EMariotte/MecanumRobot/hardware/MecanumRobot_v1.1/Schematic/MCU.kicad_sch

## KiCad design hardware/MecanumRobot_v1.1/Schematic/MCU.kicad_sch (2026-06-23)

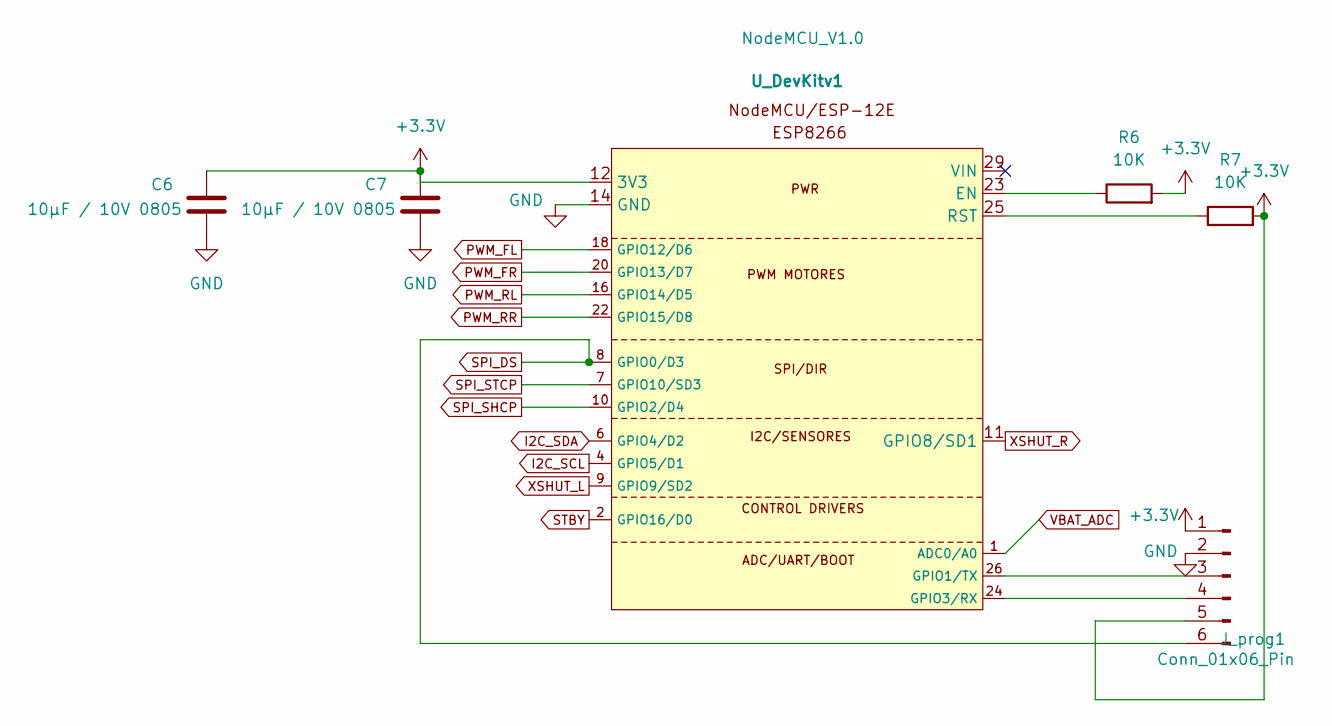
[picture p2: schematic MCU.kicad_sch]

Parts:
C6, C7: 10µF / 10V 0805; C_0805_2012Metric_Pad1.18x1.45mm_HandSolder
J_prog1: Conn_01x06_Pin; PinHeader_1x06_P2.54mm_Vertical
R6, R7: 10K; R_0805_2012Metric_Pad1.20x1.40mm_HandSolder
U_DevKitv1: NodeMCU_V1.0; DevKit_V1

Connections:
+3.3V: C6.1, C7.1, J_prog1.1, J_prog1.5, R6.2, R7.2, U_DevKitv1.12 (3V3)
GND: C6.2, C7.2, J_prog1.2, U_DevKitv1.14 (GND)
I2C_SCL: U_DevKitv1.4 (GPIO5/D1)
I2C_SDA: U_DevKitv1.6 (GPIO4/D2)
unnamed: J_prog1.3, U_DevKitv1.26 (GPIO1/TX)
unnamed: J_prog1.4, U_DevKitv1.24 (GPIO3/RX)
unnamed: R6.1, U_DevKitv1.23 (EN)
unnamed: R7.1, U_DevKitv1.25 (RST)
PWM_FL: U_DevKitv1.18 (GPIO12/D6)
PWM_FR: U_DevKitv1.20 (GPIO13/D7)
PWM_RL: U_DevKitv1.16 (GPIO14/D5)
PWM_RR: U_DevKitv1.22 (GPIO15/D8)
SPI_DS: J_prog1.6, U_DevKitv1.8 (GPIO0/D3)
SPI_SHCP: U_DevKitv1.10 (GPIO2/D4)
SPI_STCP: U_DevKitv1.7 (GPIO10/SD3)
STBY: U_DevKitv1.2 (GPIO16/D0)
VBAT_ADC: U_DevKitv1.1 (ADC0/A0)
XSHUT_L: U_DevKitv1.9 (GPIO9/SD2)
XSHUT_R: U_DevKitv1.11 (GPIO8/SD1)
