EMariotte/MecanumRobot/hardware/MecanumRobot_v1.1/Schematic/MOTOR.kicad_sch

## KiCad design hardware/MecanumRobot_v1.1/Schematic/MOTOR.kicad_sch (2026-06-23)

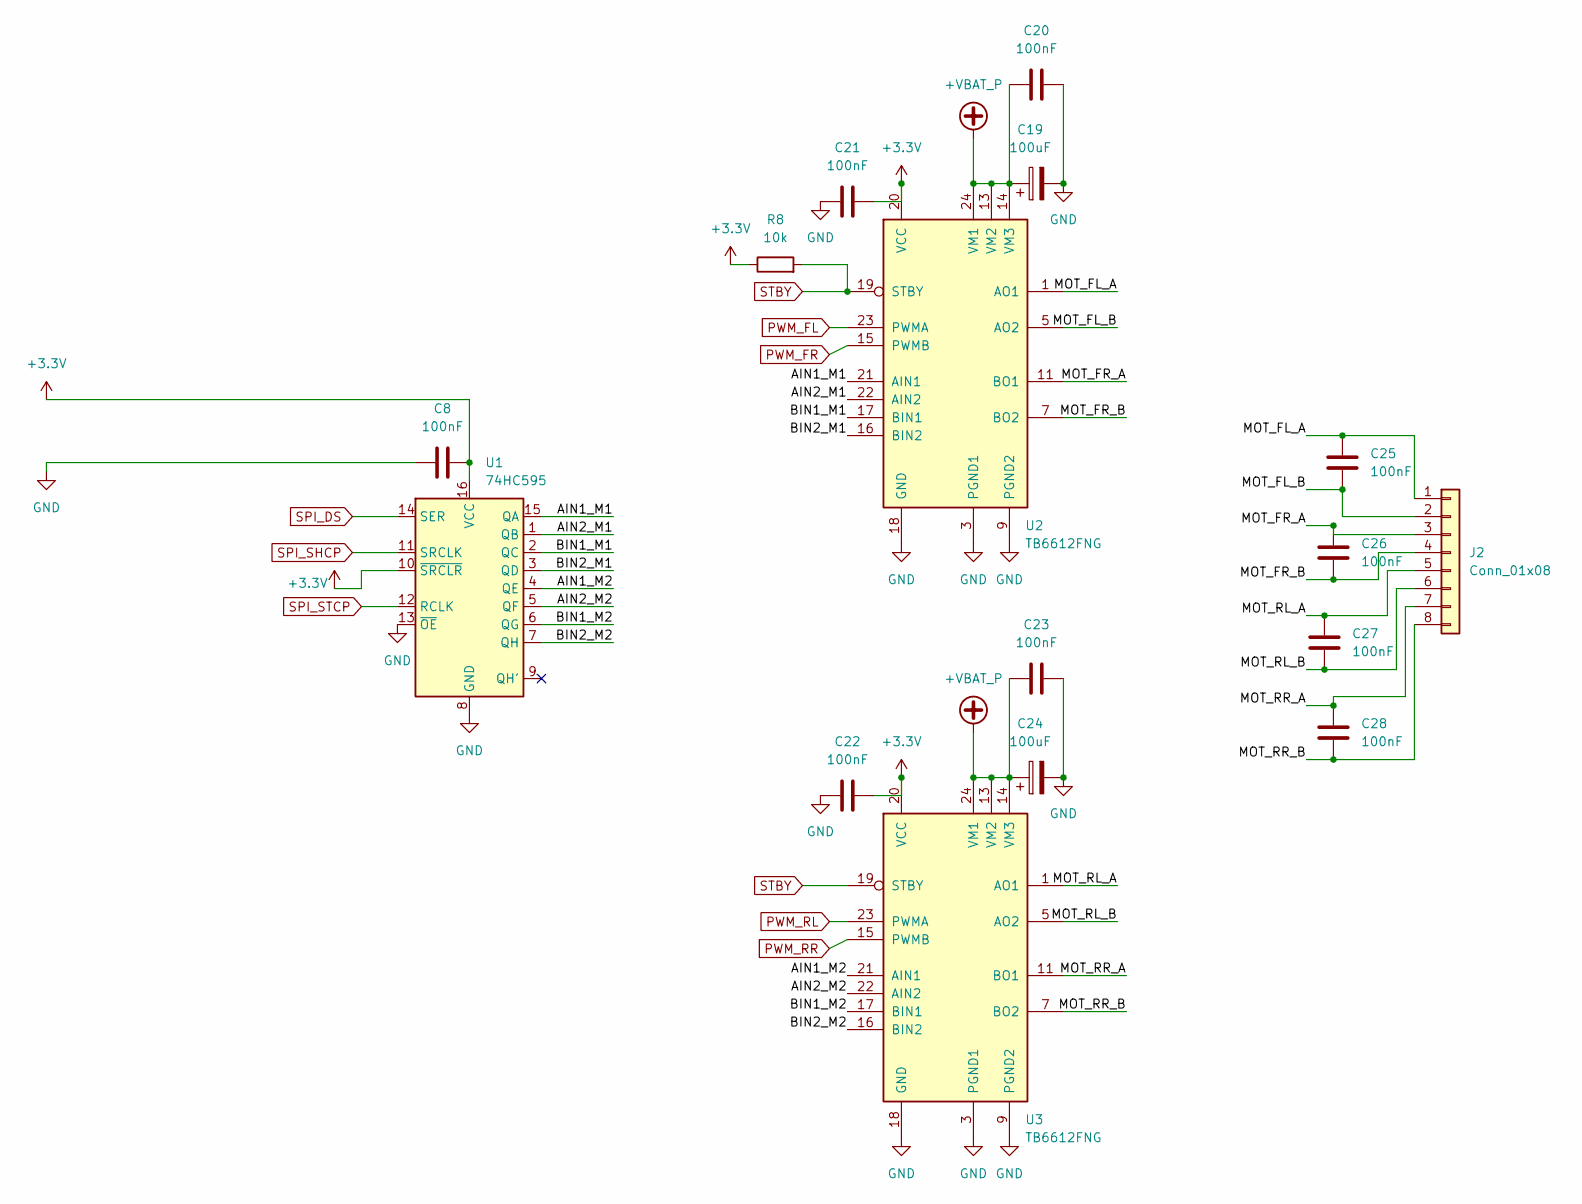
[picture p3: schematic MOTOR.kicad_sch]

Parts:
C8, C20, C23, C25, C26, C27, C28: 100nF; C_0805_2012Metric_Pad1.18x1.45mm_HandSolder
C19, C24: 100uF; CP_Elec_6.3x5.4
C21, C22: 100nF; C_1808_4520Metric_Pad1.72x2.30mm_HandSolder
J2: Conn_01x08; TerminalBlock_Phoenix_PT-1,5-8-3.5-H_1x08_P3.50mm_Horizontal
R8: 10k; R_0805_2012Metric_Pad1.20x1.40mm_HandSolder
U1: 74HC595
U2, U3: TB6612FNG; SSOP-24_5.3x8.2mm_P0.65mm

Connections:
+3.3V: C8.2, C21.2, C22.2, R8.1, U1.10 (~SRCLR), U1.16 (VCC), U2.20 (VCC), U3.20 (VCC)
+VBAT_P: C19.1, C20.1, C23.1, C24.1, U2.13 (VM2), U2.14 (VM3), U2.24 (VM1), U3.13 (VM2), U3.14 (VM3), U3.24 (VM1)
AIN1_M1: U1.15 (QA), U2.21 (AIN1)
AIN1_M2: U1.4 (QE), U3.21 (AIN1)
AIN2_M1: U1.1 (QB), U2.22 (AIN2)
AIN2_M2: U1.5 (QF), U3.22 (AIN2)
BIN1_M1: U1.2 (QC), U2.17 (BIN1)
BIN1_M2: U1.6 (QG), U3.17 (BIN1)
BIN2_M1: U1.3 (QD), U2.16 (BIN2)
BIN2_M2: U1.7 (QH), U3.16 (BIN2)
GND: C8.1, C19.2, C20.2, C21.1, C22.1, C23.2, C24.2, U1.8 (GND), U1.13 (~OE), U2.3 (PGND1), U2.4 (PGND1), U2.9 (PGND2), U2.10 (PGND2), U2.18 (GND), U3.3 (PGND1), U3.4 (PGND1), U3.9 (PGND2), U3.10 (PGND2), U3.18 (GND)
MOT_FL_A: C25.1, J2.1, U2.1 (AO1), U2.2 (AO1)
MOT_FL_B: C25.2, J2.2, U2.5 (AO2), U2.6 (AO2)
MOT_FR_A: C26.1, J2.3, U2.11 (BO1), U2.12 (BO1)
MOT_FR_B: C26.2, J2.4, U2.7 (BO2), U2.8 (BO2)
MOT_RL_A: C27.1, J2.5, U3.1 (AO1), U3.2 (AO1)
MOT_RL_B: C27.2, J2.6, U3.5 (AO2), U3.6 (AO2)
MOT_RR_A: C28.1, J2.7, U3.11 (BO1), U3.12 (BO1)
MOT_RR_B: C28.2, J2.8, U3.7 (BO2), U3.8 (BO2)
PWM_FL: U2.23 (PWMA)
PWM_FR: U2.15 (PWMB)
PWM_RL: U3.23 (PWMA)
PWM_RR: U3.15 (PWMB)
SPI_DS: U1.14 (SER)
SPI_SHCP: U1.11 (SRCLK)
SPI_STCP: U1.12 (RCLK)
STBY: R8.2, U2.19 (STBY), U3.19 (STBY)
