EMariotte/MecanumRobot/hardware/MecanumRobot_v1.1/Schematic/PWR.kicad_sch

## KiCad design hardware/MecanumRobot_v1.1/Schematic/PWR.kicad_sch (2026-06-23)

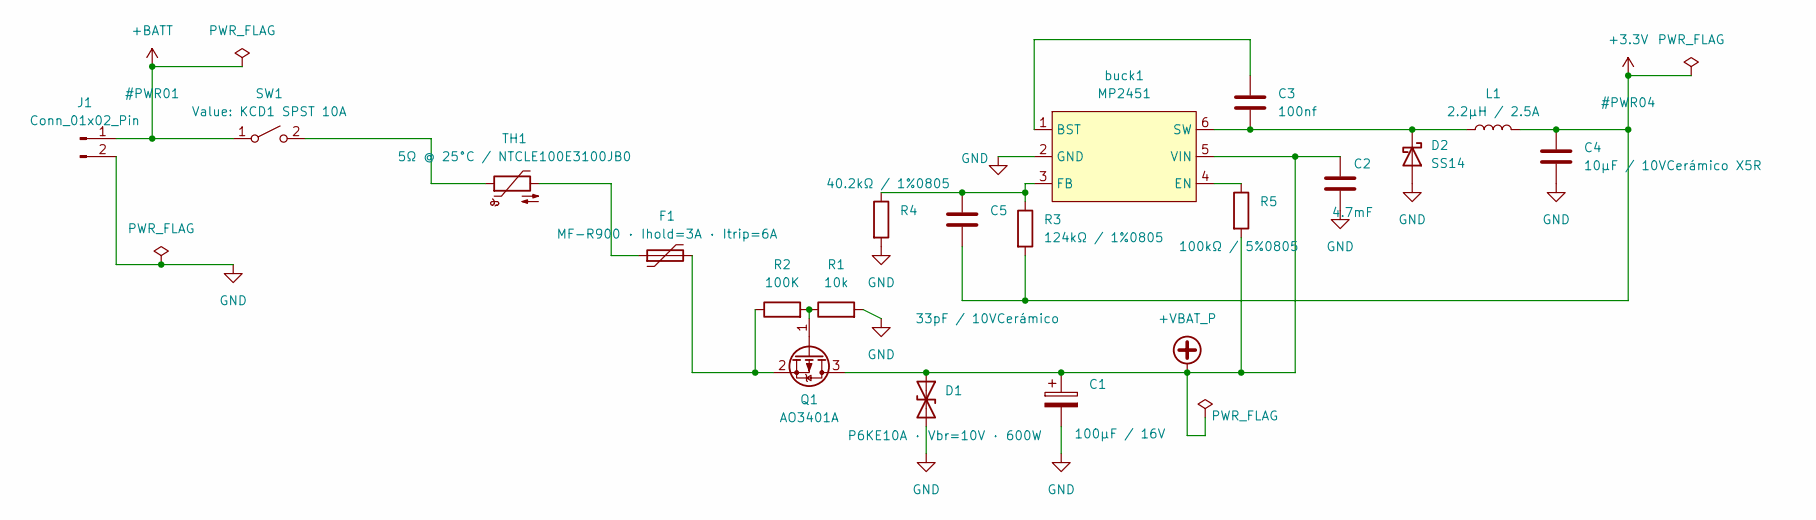
[picture p4: schematic PWR.kicad_sch]

Parts:
C1: 100µF / 16V; CP_Elec_6.3x5.4
C2: 4.7mF; C_0805_2012Metric
C3: 100nf; C_01005_0402Metric
C4: 10µF / 10VCerámico X5R; C_0805_2012Metric
C5: 33pF / 10VCerámico; C_0402_1005Metric
D1: P6KE10A · Vbr=10V · 600W; D_DO-15_P12.70mm_Horizontal
D2: SS14; D_SMA_Handsoldering
F1: MF-R900 · Ihold=3A · Itrip=6A; Fuse_2920_7451Metric
J1: Conn_01x02_Pin; PinHeader_1x02_P2.54mm_Vertical
L1: 2.2µH / 2.5A; L_Bourns_SRR1260
Q1: AO3401A; SOT-23
R1: 10k; R_0805_2012Metric_Pad1.20x1.40mm_HandSolder
R2: 100K; R_0805_2012Metric_Pad1.20x1.40mm_HandSolder
R3: 124kΩ / 1%0805; R_0805_2012Metric_Pad1.20x1.40mm_HandSolder
R4: 40.2kΩ / 1%0805; R_0805_2012Metric_Pad1.20x1.40mm_HandSolder
R5: 100kΩ / 5%0805; R_0805_2012Metric
SW1: KCD1 SPST 10A
TH1: 5Ω @ 25°C / NTCLE100E3100JB0; R_Axial_DIN0516_L15.5mm_D5.0mm_P5.08mm_Vertical
buck1: MP2451; SOT-23-5

Connections:
+3.3V: C4.1, C5.2, L1.2, R3.2
+BATT: J1.1, SW1.1 (A)
+VBAT_P: C1.1, C2.1, D1.1 (A1), Q1.3 (D), R5.2, buck1.5 (VIN)
GND: C1.2, C2.2, C4.2, D1.2 (A2), D2.2 (A), J1.2, R1.2, R4.2, buck1.2 (GND)
unnamed: C3.1, buck1.1 (BST)
unnamed: C3.2, D2.1 (K), L1.1, buck1.6 (SW)
unnamed: C5.1, R3.1, R4.1, buck1.3 (FB)
unnamed: F1.1, TH1.2
unnamed: F1.2, Q1.2 (S), R2.1
unnamed: Q1.1 (G), R1.1, R2.2
unnamed: R5.1, buck1.4 (EN)
unnamed: SW1.2 (B), TH1.1
